fitzterra/bittycade/firmware/sprites.h

#ifndef __SPRITES_H__
#define __SPRITES_H__

#include "config.h"

byte lost[] = {
  B00000000,
  B00111110,
  B01111111,
  B01001001,
  B01111111,
  B01110111,
  B00111110,
  B00101010 
};

byte up[] = {
  B00000000,
  B10101110,
  B10101010,
  B10101110,
  B10101000,
  B11101000,
  B00000000,
  B11111111
};

byte spriteMenus[NUM_GAMES][LEDMATRIX_Y] = {
  {
    B00000000,
    B00000000,
    B00000000,
    B00000100,
    B00000000,
    B00000000,
    B00000000,
    B01110000,
  }, {
    B00101010,
    B00101010,
    B00000000,
    B00000000,
    B00000000,
    B00000000,
    B00000000,
    B01000000,
  }, {
    B00000000,
    B00000010,
    B00000000,
    B00000000,
    B01100000,
    B00100010,
    B00111110,
    B00000000,
  }, {
    B11001111,
    B01011111,
    B00000000,
    B00000000,
    B00010000,
    B00000000,
    B00000000,
    B00001100,
  }, {
    B11000001,
    B10001111,
    B10000111,
    B11000011,
    B11100001,
    B11110001,
    B11100001,
    B10000101,
  }
};

byte lights[] = {
  B01010101,
  B10101010
};

byte track[] = {
B10000001,
B10000001,
B10000001,
B10000001,
B10000001,
B10000001,
B10000001,
B10000001,
B10011111,
B10011111,
B10000001,
B10000001,
B10000001,
B10000001,
B11111001,
B11111001,
B10000001,
B10000001,
B10000001,
B10000001,
B10001111,
B10001111,
B10000001,
B10000001,
B10000001,
B10000001,
B11110001,
B11110001,
B10000001,
B10000001,
B10000001,
B10000001,
B10000001,
B10001001,
B10001001,
B10011001,
B10011001,
B10011001,
B10011001,
B10010001,
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
};			
			
uint16_t TRACKLEN = sizeof(track)/sizeof(byte);
#endif // __SPRITES_H__
